GhostRoboticsLab/Hackagotchi/firmware/c/src/sd_gate.c

/*
 * Hackagotchi — M2 SD/recorder task. SPDX-License-Identifier: MIT  (see sd_gate.h)
 *
 * The single FatFs caller. At boot it runs the SD bring-up self-test (mount + write + read-back,
 * reported via CDC1 {"q":"sd"}), then becomes the black-box recorder: drains the recorder ring that
 * cdc_task tees into, runs the recorder core (recorder.c) against the carlk3 FatFs seam, and logs the
 * target UART to session files. LOW priority (idle+0, below DAP) — every FatFs/SPI op stays off the
 * DAP/USB hot path (R1). All recorder_t state is owned here (no other task touches it).
 */

#include "sd_gate.h"

#include <stdio.h>
#include <stdlib.h>   // atoi
#include <string.h>
#include <pico/stdlib.h>

#include "ff.h"            // ChaN FatFs (carlk3)
#include "probe_config.h"  // PROBE_UART_BAUDRATE (header baud)
#include "recorder.h"
#include "uart_bridge.h"
#include "feedback.h"      // M3.0: non-blocking LED/buzzer service (serviced from this low-prio task)
#include "hg_config.h"     // M4.5: persisted baud + macros (KV config file on the SD card)
#include "hackagotchi_dashboard.h"   // M4.1: dash_hex_mode() — gate the per-loop raw-tail copy
#include "hg_input.h"                // v1.2: poll the button here (20 ms, GPIO only — no bus, no mutex)

TaskHandle_t sd_gate_taskhandle;

#define SD_TEST_PATH "hg_sdgate.txt"

// --- bring-up self-test result (gate; {"q":"sd"}) ---
static volatile bool     s_done = false, s_mounted = false, s_write_ok = false, s_readback_ok = false;
static volatile uint32_t s_bytes = 0, s_free_kb = 0;
static volatile int      s_fr = -1;

static FATFS s_fs;   // the one mount, owned by this task

static void run_selftest(void) {
    static FIL fil;
    char line[64];
    int n = snprintf(line, sizeof line, "HACKAGOTCHI SD GATE up=%lu\n",
                     (unsigned long)(time_us_64() / 1000000ull));
    FRESULT fr = f_mount(&s_fs, "", 1);
    s_fr = (int)fr;
    if (fr != FR_OK) { s_done = true; return; }
    s_mounted = true;
    fr = f_open(&fil, SD_TEST_PATH, FA_CREATE_ALWAYS | FA_WRITE);
    if (fr == FR_OK) {
        UINT bw = 0;
        fr = f_write(&fil, line, (UINT)n, &bw);
        f_close(&fil);
        s_bytes = bw;
        if (fr == FR_OK && bw == (UINT)n) s_write_ok = true;
    }
    s_fr = (int)fr;
    if (s_write_ok) {
        fr = f_open(&fil, SD_TEST_PATH, FA_READ);
        if (fr == FR_OK) {
            char rb[64]; UINT br = 0;
            fr = f_read(&fil, rb, sizeof rb, &br);
            f_close(&fil);
            if (fr == FR_OK && br == (UINT)n && memcmp(rb, line, (size_t)n) == 0) s_readback_ok = true;
        }
        s_fr = (int)fr;
    }
    DWORD fre = 0; FATFS *fsp = NULL;
    if (f_getfree("", &fre, &fsp) == FR_OK && fsp)
        s_free_kb = (uint32_t)((uint64_t)fre * fsp->csize * 512ull / 1024ull);
    s_done = true;
}

// ---- recorder_hw_t seam wired to carlk3 FatFs (this task is the ONLY FatFs caller) ----
static recorder_t g_rec;
static FIL        s_log_fil;          // reused per flush (open-append -> write -> close)
static FRESULT    s_log_fr = FR_OK;
static char       s_alert[24] = "";   // last recorder alert (M3: buzzer/LED; for now a CDC1 badge)

static bool  hw_mounted(void) { return s_mounted; }
static int   hw_max_log_index(void) {
    DIR dir; FILINFO fno; int mx = 0;
    if (f_findfirst(&dir, &fno, "", "log_*.txt") == FR_OK) {
        while (fno.fname[0]) {
            int v = atoi(fno.fname + 4);   // "log_" is 4 chars -> NNN
            if (v > mx) mx = v;
            if (f_findnext(&dir, &fno) != FR_OK) break;
        }
        f_closedir(&dir);
    }
    return mx;
}
static void *hw_open_append(const char *name) {
    s_log_fr = f_open(&s_log_fil, name, FA_OPEN_APPEND | FA_WRITE);
    return (s_log_fr == FR_OK) ? &s_log_fil : NULL;
}
static int hw_write(void *h, const void *buf, size_t n) {
    UINT bw = 0;
    s_log_fr = f_write((FIL *)h, buf, (UINT)n, &bw);
    return (s_log_fr == FR_OK) ? (int)bw : -1;
}
static void hw_close(void *h) { f_close((FIL *)h); }            // close flushes -> durable per session-flush
static bool hw_fault_full(void) { return s_log_fr == FR_DENIED; }  // FatFs "disk full"
static void hw_alert(const char *text, int lo, int hi) {
    (void)lo; (void)hi;
    snprintf(s_alert, sizeof s_alert, "%s", text);
}
// rtc_read = NULL: the RTC was dropped, so the recorder stamps log lines with the uptime fallback
// ("+Ns") — recorder.c's stamp() null-checks the seam (this build has no wall-clock device).
static const recorder_hw_t REC_HW = {
    hw_mounted, hw_max_log_index, hw_open_append, hw_write, hw_close, hw_fault_full, NULL, hw_alert
};

// ---- async tail read (CDC1 {"q":"tail"} content proof; the read happens HERE, off the hot path) ----
static volatile bool   s_tail_req = false;
static char            s_tail_buf[192];
static volatile size_t s_tail_len = 0;

static void do_tail_read(void) {
    FIL f;
    s_tail_len = 0;
    if (f_open(&f, g_rec.filename, FA_READ) != FR_OK) return;
    FSIZE_t sz = f_size(&f);
    FSIZE_t off = (sz > sizeof s_tail_buf) ? sz - sizeof s_tail_buf : 0;
    UINT br = 0;
    if (f_lseek(&f, off) == FR_OK) f_read(&f, s_tail_buf, sizeof s_tail_buf, &br);
    f_close(&f);
    s_tail_len = br;
}

// ---- async SD explorer (M4.4): list log files / read a file page. SD-task-owned, off the hot path,
// same request -> read-on-a-later-call pattern as the tail. ----
static volatile bool   s_ls_req = false;
static char            s_ls_buf[400];   // pre-formatted JSON array body: "log_000.txt","log_001.txt",...
static volatile size_t s_ls_len = 0;
static volatile int    s_ls_count = 0;  // total log_*.txt files (>= the number listed)
static int             s_log_count = 0; // cached total, published in the snapshot (SD-EXPLORER screen)

static void do_ls_read(void) {
    DIR dir; FILINFO fno;
    size_t o = 0; int n = 0, listed = 0;
    if (f_findfirst(&dir, &fno, "", "log_*.txt") == FR_OK) {
        while (fno.fname[0]) {
            n++;
            if (listed < 24) {
                // snprintf returns the WOULD-BE length; with FF_USE_LFN a card-supplied long name matching
                // log_*.txt could exceed the buffer, so advance o ONLY if the entry actually fit (no OOB).
                int w = snprintf(s_ls_buf + o, sizeof s_ls_buf - o, "%s\"%s\"", listed ? "," : "", fno.fname);
                if (w >= 0 && (size_t)w < sizeof s_ls_buf - o) { o += (size_t)w; listed++; }
                else listed = 24;   // won't fit -> stop listing (keep counting n); s_ls_buf[o] stays in bounds
            }
            if (f_findnext(&dir, &fno) != FR_OK) break;
        }
        f_closedir(&dir);
    }
    s_ls_buf[o] = '\0';
    s_ls_len = o;
    s_ls_count = n;
    s_log_count = n;
}

static volatile bool     s_cat_req = false;
static char              s_cat_file[16];  // "log_NNN.txt" built from a numeric index (no path traversal)
static volatile uint32_t s_cat_off = 0;
static char              s_cat_buf[160];
static volatile size_t   s_cat_len = 0;
static volatile bool     s_cat_eof = false;

static void do_cat_read(void) {
    FIL f; s_cat_len = 0; s_cat_eof = true;
    if (f_open(&f, s_cat_file, FA_READ) != FR_OK) return;
    FSIZE_t sz = f_size(&f);
    UINT br = 0;
    if ((FSIZE_t)s_cat_off < sz && f_lseek(&f, s_cat_off) == FR_OK)
        f_read(&f, s_cat_buf, sizeof s_cat_buf, &br);
    f_close(&f);
    s_cat_len = br;
    s_cat_eof = ((FSIZE_t)s_cat_off + br >= sz);
}

// ---- M4.5 settings persistence: load/save the KV config file on the SD card (SD-task-owned I/O) ----
#define HG_CONFIG_FILE "config.txt"
static volatile bool s_cfg_save_req = false;
void sd_config_save_request(void) { s_cfg_save_req = true; }

static void do_config_load(void) {
    FIL f; char buf[256]; UINT br = 0;
    if (f_open(&f, HG_CONFIG_FILE, FA_READ) != FR_OK) return;   // absent on first boot -> defaults stand
    f_read(&f, buf, sizeof buf - 1, &br); f_close(&f);
    hg_config_apply_kv(buf, br);
}

static void do_config_save(void) {
    char buf[256]; int n = hg_config_serialize(buf, sizeof buf);
    if (n <= 0) return;
    FIL f;
    if (f_open(&f, HG_CONFIG_FILE, FA_CREATE_ALWAYS | FA_WRITE) != FR_OK) return;
    UINT bw = 0; f_write(&f, buf, (UINT)n, &bw); f_close(&f);
}

// Device-side recorder load generator (HIL hook for the SD-during-flash coexistence soak). When on,
// the SD task synthesizes recorder data every loop -> continuous f_write/f_sync to the card, with NO
// host UART traffic. A concurrent probe-rs flash soak then measures pure SD-vs-DAP contention, without
// the host driving both DAP and a CDC0 stream (the confound that made the host-injection version useless).
static volatile bool s_recgen;
static uint32_t s_recgen_seq;
void sd_recgen_set(bool on) { s_recgen = on; }

// ---- M3 published recorder snapshot (single-writer seqlock; see sd_gate.h) ----
// Writer = THIS task only (publish_snapshot, once per loop after recorder_tick, when g_rec is internally
// consistent). Readers = the dashboard render loop + the CDC1 {"q":"rec"} reply. seq is even when stable,
// odd while being written; a reader retries until it copies across a stable, unchanged seq. The fences
// are belt-and-braces (the real protection on single-core RP2040 is the seq-retry against preemption).
static volatile uint32_t s_snap_seq = 0;
static rec_snapshot_t    s_snap;            // the published copy
static uint16_t          s_revived = 0;     // M-UI-5: wedge->recover edges, counted here (50 Hz) so a
static uint16_t          s_faults  = 0;     //   fast edge isn't missed by the 4 Hz dashboard; published.

static void publish_snapshot(void) {
    rec_snapshot_t s;
    memset(&s, 0, sizeof s);
    if (s_mounted) {   // recorder_init/start only ran if mounted; g_rec.hw is NULL otherwise
        recorder_status_t st;
        recorder_get_status(&g_rec, &st);                       // SAFE: this IS the owning task
        s.logging  = st.logging;  s.wedge   = st.wedge;
        s.rx_total = st.rx_total; s.hits    = st.hits;
        s.tp_peak  = st.tp_peak;  s.last_err = (int)st.last_err;
        snprintf(s.file, sizeof s.file, "%s", st.log_file);     // bounded copy, not a live pointer
        recorder_copy_tail(&g_rec, sizeof s.tail - 1, s.tail, sizeof s.tail);
        if (dash_hex_mode())   // M4.1: only pay the raw-byte copy when the hex view is actually shown
            s.rawn = (uint8_t)recorder_copy_raw_tail(&g_rec, sizeof s.raw, s.raw, sizeof s.raw);
    }
    s.sd_mounted = s_mounted;
    s.log_count  = (uint16_t)s_log_count;   // M4.4: cached log_*.txt count for the SD-EXPLORER screen
    s.rec_drop   = uart_bridge_rec_drops();
    s.revived    = s_revived;   // M-UI-5: resurrection tally (edge-counted in drive_feedback)
    s.faults     = s_faults;
    snprintf(s.alert, sizeof s.alert, "%s", s_alert);

    s_snap_seq++;                              // -> odd (write in progress)
    __atomic_thread_fence(__ATOMIC_RELEASE);
    s_snap = s;
    __atomic_thread_fence(__ATOMIC_RELEASE);
    s_snap_seq++;                              // -> even (stable)
}

bool dash_get_rec_snapshot(rec_snapshot_t *out) {
    for (int tries = 0; tries < 16; tries++) {
        uint32_t s1 = s_snap_seq;
        if (s1 & 1u) continue;                 // writer mid-update
        __atomic_thread_fence(__ATOMIC_ACQUIRE);
        *out = s_snap;
        __atomic_thread_fence(__ATOMIC_ACQUIRE);
        if (s1 == s_snap_seq) return true;     // unchanged across the copy
    }
    return false;
}

// M3.3 — map recorder events to the buzzer + NeoPixel (non-blocking, via the feedback HAL). Called each
// loop from the OWNING task, so recorder_get_status(&g_rec) is race-free here. The status COLOUR is set
// only on change (green=recording OK, red=wedge/fault), so CDC1 pixel/led tests can coexist between
// events; the buzzer fires on EDGES only (wedge alarm / recovery chirp / SD-fault buzz / trigger blip).
static void drive_feedback(void) {
    if (!s_mounted) return;
    static bool     first = true, last_wedge = false, last_err = false, last_rx = false;
    static uint32_t last_hits = 0, last_color = 0xFFFFFFFFu;
    recorder_status_t st;
    recorder_get_status(&g_rec, &st);
    bool err = (st.last_err != REC_ERR_NONE);
    bool rx_seen = (st.rx_total > 0);

    if (!first) {
        if (rx_seen && !last_rx)          feedback_beep(1700, 70);    // M-UI-5: ghost summon (the target's first words)
        if (st.wedge && !last_wedge)      feedback_beep(700, 500);    // target wedged -> alarm (death rattle)
        else if (!st.wedge && last_wedge) { feedback_beep(2200, 80); s_revived++; }  // recovered -> chirp (gasp)
        if (err && !last_err)             { feedback_beep(500, 700);  s_faults++;  }  // SD write/full fault -> buzz
        if (st.hits > last_hits)          feedback_beep(2600, 70);    // trigger-term hit -> blip
    }
#if defined(HG_NEOPIXEL_COUNT) && (HG_NEOPIXEL_COUNT > 1)
    // v1.2 "Companion": an external WS2812 chain shows a reactive MOOD instead of a single status colour.
    // fault > recent-traffic > logging > off. RX latches for 1.5 s so the green pulse outlives a burst.
    static uint32_t active_until = 0, last_rx_total = 0;
    uint32_t now = (uint32_t)(time_us_64() / 1000ull);
    if (st.rx_total > last_rx_total) { active_until = now + 1500u; last_rx_total = st.rx_total; }
    int mood = (st.wedge || err)     ? NP_MOOD_FAULT
             : (now < active_until)  ? NP_MOOD_RX
             : (st.logging)          ? NP_MOOD_IDLE
                                     : NP_MOOD_OFF;
    feedback_mood(mood, 200);
    (void)last_color;
#else
    uint32_t color = (st.wedge || err) ? 0x400000u : (st.logging ? 0x001000u : 0u);  // red / dim green / off
    if (color != last_color) {
        feedback_pixel((uint8_t)(color >> 16), (uint8_t)(color >> 8), (uint8_t)color);
        last_color = color;
    }
#endif
    last_wedge = st.wedge; last_err = err; last_hits = st.hits; last_rx = rx_seen; first = false;
}

void sd_gate_task(void *ptr) {
    (void)ptr;
    run_selftest();
    if (s_mounted) {
        do_config_load();                            // M4.5: restore persisted baud + macros first
        cdc_uart_set_baud_request(hg_baud());        // apply the (possibly restored) baud to the target UART
        recorder_init(&g_rec, &REC_HW, hg_baud());   // session header reflects the actual baud
        recorder_start(&g_rec, (uint32_t)(time_us_64() / 1000ull));   // auto-start logging at boot
        feedback_beep(2000, 60);   // M3.3: a single "alive" chirp at boot (full jingles -> UI rewrite)
        do_ls_read();              // M4.4: populate the cached log count for the SD-EXPLORER screen
    }
    static uint8_t drain[256];
    for (;;) {
        uint32_t now = (uint32_t)(time_us_64() / 1000ull);
        size_t n = uart_bridge_rec_read(drain, sizeof drain);
        if (n) recorder_feed(&g_rec, drain, n, now);
        if (s_recgen) {   // synthetic continuous SD-write load (coexistence soak); ~107 B/iter @ ~50 Hz
            static char gen[160];
            int gl = snprintf(gen, sizeof gen,
                "RECGEN %08lu the-quick-brown-fox-jumps-over-the-lazy-dog-0123456789-ABCDEFGHIJKLMNOPQRSTUVWXYZ\n",
                (unsigned long)s_recgen_seq++);
            if (gl > 0) recorder_feed(&g_rec, (const uint8_t *)gen, (size_t)gl, now);
        }
        recorder_tick(&g_rec, now, uart_bridge_rx_last_ms(), uart_bridge_rx_ever());
        if (s_tail_req) { do_tail_read(); s_tail_req = false; }
        if (s_ls_req)   { do_ls_read();   s_ls_req = false; }   // M4.4 SD explorer (async, off the hot path)
        if (s_cat_req)  { do_cat_read();  s_cat_req = false; }
        if (s_cfg_save_req) { do_config_save(); s_cfg_save_req = false; }   // M4.5 persist on change
        publish_snapshot();          // M3: hand the dashboard + CDC1 a consistent copy of recorder state
        drive_feedback();            // M3.3: map recorder events -> buzzer + NeoPixel (edge-detected)
        hg_button_poll(now);         // v1.2: debounce the GP16 button (no-op unless HG_BUTTON) -> nav/pet
        feedback_service(now);       // M3.0: apply the latched beep/pixel + buzzer-off, off the hot path
        vTaskDelay(pdMS_TO_TICKS(20));
    }
}

void sd_gate_status_json(char *out, unsigned outsz) {
    snprintf(out, outsz,
             "{\"sd\":%d,\"done\":%d,\"write\":%d,\"readback\":%d,"
             "\"bytes\":%u,\"free_kb\":%u,\"fr\":%d}\n",
             (int)s_mounted, (int)s_done, (int)s_write_ok, (int)s_readback_ok,
             (unsigned)s_bytes, (unsigned)s_free_kb, (int)s_fr);
}

void sd_rec_status_json(char *out, unsigned outsz) {
    // M3: read the SD-task-published snapshot, NOT g_rec directly. The old version called
    // recorder_get_status(&g_rec) from the TUD task — handing out a live pointer into g_rec.filename
    // (rewritten by recorder_start mid-snprintf -> torn/unterminated read) and calling hw->sd_mounted()
    // off the owning task. The snapshot closes that race for both this reply and the dashboard.
    rec_snapshot_t s;
    if (!dash_get_rec_snapshot(&s)) { snprintf(out, outsz, "{\"err\":\"busy\"}\n"); return; }
    snprintf(out, outsz,
             "{\"logging\":%d,\"file\":\"%s\",\"rx\":%u,\"wedge\":%d,\"hits\":%u,"
             "\"err\":%d,\"tp_peak\":%u,\"rec_drop\":%u,\"alert\":\"%s\"}\n",
             (int)s.logging, s.file, (unsigned)s.rx_total, (int)s.wedge,
             (unsigned)s.hits, s.last_err, (unsigned)s.tp_peak,
             (unsigned)s.rec_drop, s.alert);
}

void sd_rec_tail_request(void) { s_tail_req = true; }

void sd_rec_tail_json(char *out, unsigned outsz) {
    // emit the captured tail as a JSON string with non-printables escaped to '.'
    size_t len = s_tail_len;
    if (len > 160) len = 160;
    char esc[164];
    size_t o = 0;
    for (size_t i = 0; i < len && o + 1 < sizeof esc; i++) {
        char c = s_tail_buf[i];
        esc[o++] = (c >= 32 && c <= 126 && c != '"' && c != '\\') ? c : '.';
    }
    esc[o] = '\0';
    snprintf(out, outsz, "{\"tail_len\":%u,\"tail\":\"%s\"}\n", (unsigned)s_tail_len, esc);
}

// ---- M4.4 SD explorer public API (request -> read on a later call, like the tail) ----
void sd_ls_request(void) { s_ls_req = true; }

void sd_ls_json(char *out, unsigned outsz) {
    snprintf(out, outsz, "{\"ls\":[%s],\"n\":%d,\"shown\":%d}\n",
             s_ls_buf, s_ls_count, (s_ls_count > 24 ? 24 : s_ls_count));
}

void sd_cat_request(int idx, uint32_t off) {
    if (idx < 0) idx = 0;
    snprintf(s_cat_file, sizeof s_cat_file, "log_%03d.txt", idx);  // index -> name (no path traversal)
    s_cat_off = off;
    s_cat_req = true;
}

void sd_cat_json(char *out, unsigned outsz) {
    size_t len = s_cat_len;
    if (len > 152) len = 152;
    char esc[160]; size_t o = 0;
    for (size_t i = 0; i < len && o + 1 < sizeof esc; i++) {
        char c = s_cat_buf[i];
        esc[o++] = (c >= 32 && c <= 126 && c != '"' && c != '\\') ? c : '.';
    }
    esc[o] = '\0';
    snprintf(out, outsz, "{\"file\":\"%s\",\"off\":%lu,\"len\":%u,\"eof\":%d,\"data\":\"%s\"}\n",
             s_cat_file, (unsigned long)s_cat_off, (unsigned)s_cat_len, s_cat_eof ? 1 : 0, esc);
}
