GhostRoboticsLab/Hackagotchi/firmware/c/src/watchdog_task.c

/*
 * Hackagotchi — M1 reliability core: software watchdog task. SPDX-License-Identifier: MIT
 * See watchdog_task.h for the rationale (monitor the high-prio TUD task; armed by default).
 */

#include "watchdog_task.h"
#include "crash_box.h"

#include <pico/stdlib.h>
#include "hardware/watchdog.h"

#define WD_FEED_MS        500u   // health-task period: feed the HW WDT + sample the heartbeat
#define WD_HW_TIMEOUT_MS 8000u   // HW WDT timeout — backstop for the health task ITSELF wedging
#define WD_TUD_STALL_MS  4000u   // TUD must check in within this window or it is declared wedged

TaskHandle_t watchdog_taskhandle;

// ARMED BY DEFAULT (the shipping posture — the probe must never sit silently wedged). Safe because we
// monitor the TUD task (prio +2), which is high-priority and always servicing USB: DAP (prio +1) is
// LOWER, so flash load can never starve TUD, and TUD goes silent only on a true wedge. Soak-proven
// (tests/m1/M1_RESULTS.md, increment 5) to not false-fire under sustained DAP + USB load.
static volatile bool s_armed = true;

// DIAGNOSTIC telemetry: peak observed TUD stall (max since_ms, 500 ms granularity). Stays 0 while TUD
// advances within every sample window; a non-zero value means TUD genuinely missed window(s). Exposed
// in status (and resettable via wd_reset) for observability — NOT a continuous "margin" (the heartbeat
// free-runs, so no normal load can drive this above 0), so tests report it, they do not gate on it.
static volatile uint32_t s_max_gap_ms = 0;

void wd_arm(void)         { s_armed = true; }
bool wd_is_armed(void)    { return s_armed; }
uint32_t wd_max_gap_ms(void) { return s_max_gap_ms; }
void wd_gap_reset(void)   { s_max_gap_ms = 0; }  // zero the peak so a test measures only its own run

void watchdog_task(void *ptr) {
    (void)ptr;

    uint32_t last_checkin = 0;
    uint32_t since_ms = 0;
    bool hw_on = false;
    TickType_t wake = xTaskGetTickCount();

    for (;;) {
        if (s_armed) {
            if (!hw_on) {
                // Arm on the first armed cycle: enable the HW WDT and start fresh from the current
                // heartbeat (so arming never inherits a stale "already stalled" reading).
                last_checkin = g_tud_checkin;
                since_ms = 0;
                watchdog_enable(WD_HW_TIMEOUT_MS, 1);  // pause_on_debug = 1
                hw_on = true;
            }

            uint32_t now = g_tud_checkin;
            if (now != last_checkin) {
                last_checkin = now;
                since_ms = 0;
            } else {
                since_ms += WD_FEED_MS;
            }
            if (since_ms > s_max_gap_ms) s_max_gap_ms = since_ms;  // measured worst-case margin

            if (since_ms >= WD_TUD_STALL_MS)
                crash_box_record_watchdog("TUD");  // records the reason, then reboots — no return

            watchdog_update();  // we reached here => the health task is alive; feed the HW WDT
        }
        // Disarmed: fully inert — the HW WDT is never enabled, so no reboot can occur.

        xTaskDelayUntil(&wake, pdMS_TO_TICKS(WD_FEED_MS));
    }
}
